ryomuk/TangNano6100MEM/hdl/TangNano6100MEM_project/src/mem_cp.v

// mem_cp.v
// to be included from the top module at the compile

initial
begin
mem_cp['o0000]='o0000;
mem_cp['o0001]='o0000;
mem_cp['o0002]='o0000;
mem_cp['o0003]='o0000;
mem_cp['o0004]='o0000;
mem_cp['o0005]='o0000;
mem_cp['o0006]='o0000;
mem_cp['o0007]='o0000;
mem_cp['o0010]='o0000;
mem_cp['o0011]='o0000;
mem_cp['o0012]='o0000;
mem_cp['o0013]='o0000;
mem_cp['o0014]='o0000;
mem_cp['o0015]='o0000;
mem_cp['o0016]='o0000;
mem_cp['o0017]='o0000;
mem_cp['o0020]='o0000;
mem_cp['o0021]='o0000;
mem_cp['o0022]='o0000;
mem_cp['o0023]='o0000;
mem_cp['o0024]='o0000;
mem_cp['o0025]='o0000;
mem_cp['o0026]='o0000;
mem_cp['o0027]='o0000;
mem_cp['o0030]='o0000;
mem_cp['o0031]='o0000;
mem_cp['o0032]='o0000;
mem_cp['o0033]='o0000;
mem_cp['o0034]='o0000;
mem_cp['o0035]='o0000;
mem_cp['o0036]='o0000;
mem_cp['o0037]='o0000;
mem_cp['o0040]='o0000;
mem_cp['o0041]='o0000;
mem_cp['o0042]='o0000;
mem_cp['o0043]='o0000;
mem_cp['o0044]='o0000;
mem_cp['o0045]='o0000;
mem_cp['o0046]='o0000;
mem_cp['o0047]='o0000;
mem_cp['o0050]='o0000;
mem_cp['o0051]='o0000;
mem_cp['o0052]='o0000;
mem_cp['o0053]='o0000;
mem_cp['o0054]='o0000;
mem_cp['o0055]='o0000;
mem_cp['o0056]='o0000;
mem_cp['o0057]='o0000;
mem_cp['o0060]='o0000;
mem_cp['o0061]='o0000;
mem_cp['o0062]='o0000;
mem_cp['o0063]='o0000;
mem_cp['o0064]='o0000;
mem_cp['o0065]='o0000;
mem_cp['o0066]='o0000;
mem_cp['o0067]='o0000;
mem_cp['o0070]='o0000;
mem_cp['o0071]='o0000;
mem_cp['o0072]='o0000;
mem_cp['o0073]='o0000;
mem_cp['o0074]='o0000;
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
mem_cp['o7764]='o0000;
mem_cp['o7765]='o0000;
mem_cp['o7766]='o0000;
mem_cp['o7767]='o0000;
mem_cp['o7770]='o0000;
mem_cp['o7771]='o0000;
mem_cp['o7772]='o0000;
mem_cp['o7773]='o0000;
mem_cp['o7774]='o0000;
mem_cp['o7775]='o0000;
mem_cp['o7776]='o5000;
mem_cp['o7777]='o5776;
end
