ryomuk/TangNano6100MEM/hdl/TangNano6100MEM_project/src/sdtape.v

// sdtape.v
// Tape reader/puncher emulator using SD/SDHC memory
// by Ryo Mukai
// 2024/05/22: initial version
// 2024/06/19: bugfixed (in S_INIT_ACMD41)
// 2025/09/20: card detect(i_sd_det_n) installed
// 2025/09/25: separate read tape(0GB-)  and write tape(1GB-)
// 2025/10/07: sd_error is ERROR_RESET during reset
// 2026/01/31: modified for IM6100 (i_tape_start_block)
// 2026/02/01: end of tape flag o_tape_eot installed

module sdtape
  #(
    parameter SYS_FRQ = 27_000_000, // system clock frequency(Hz)
    parameter MEM_FRQ =    400_000  // memory clock frequency(Hz)(106k to 1M)
    )
  (
   input	 i_clk,		     // system clock input
   input	 i_reset_n,	     // synchronous reset input, active low
   input	 i_sd_det_n,	     // card detect input, active low
   input	 i_sd_miso,
   output	 o_sd_mosi,
   output	 o_sd_cs_n,
   output	 o_sd_clk,

   output	 o_tape_read_busy,   // PR_BUSY
   output reg	 o_tape_read_done,   // PR_DONE
   output	 o_tape_punch_ready, // PP_READY
   input	 i_tape_read,	     // tape_read
   input	 i_tape_punch,	     // tape_punch
   input	 i_tape_clear_done,  // tape_clear_done
   input [7:0]	 i_tape_punch_data,  // PPBUF
   output [7:0]	 o_tape_read_data,   // PRBUF
   input	 i_tape_flush,	     //
   input [21:0]	 i_tape_start_block,
   input [21:0]	 i_tape_start_block_write,
   input	 i_tape_rewind,
   output	 o_tape_endoftape,
   output [4:0]	 o_sd_state,
   output [3:0]	 o_sd_error,
   output [30:0] o_sd_tape_address,
   output [30:0] o_sd_tape_address_write
   );

  assign o_sd_tape_address       = tape_address; // for debug
  assign o_sd_tape_address_write = tape_address_write; // for debug
  
  reg [30:0]	tape_address;        // 0GB-2GB
  reg [30:0]	tape_address_write;  // 1GB-2GB

  reg [23:0]	sd_block_address;
  reg [23:0]	sd_block_address_write;
  reg [7:0]	tape_read_buf;
  reg [7:0]	tape_punch_buf;

  assign o_tape_read_data = tape_read_buf;
  
  localparam   CLK_DIV  = SYS_FRQ / MEM_FRQ;
  localparam   CLK_DIV2 = CLK_DIV / 2;

  localparam   S_INIT_RESET      = 5'd0;
  localparam   S_INIT_DUMMY      = 5'd1;
  localparam   S_INIT_CMD0       = 5'd2;
  localparam   S_INIT_CMD8       = 5'd3;
  localparam   S_INIT_CMD55      = 5'd4;
  localparam   S_INIT_ACMD41     = 5'd5;
  localparam   S_INIT_ACMD41_RTY = 5'd6;
  localparam   S_INIT_CMD58      = 5'd7;
  localparam   S_INIT_CMD16      = 5'd8;
  localparam   S_IDLE            = 5'd9;
  localparam   S_READ_CMD        = 5'd10; // CMD17
  localparam   S_READ_DATA       = 5'd11;
  localparam   S_WRITE_CMD       = 5'd12; // CMD24
  localparam   S_WRITE_DATA      = 5'd13;
  localparam   S_WRITE_BUSY      = 5'd14;
  localparam   S_WAIT            = 5'd15;
  localparam   S_ERROR           = 5'd16;
  localparam   S_NOCARD          = 5'd17;

  reg [1:0]    sd_version;
  localparam   SD_VERSION1 = 2'd1;
  localparam   SD_VERSION2 = 2'd2;

  reg	       sd_read;
  reg	       sd_write;

  reg	       sd_addressmode_block;
  wire [31:0]  sd_address = sd_addressmode_block ?
	       {8'h0000, sd_block_address[23:0]} :
	       {sd_block_address[22:0], 9'b0};

  wire [31:0]  sd_address_write = sd_addressmode_block ?
	       {8'h0000, sd_block_address_write[23:0]} :
	       {sd_block_address_write[22:0], 9'b0};


  reg [3:0]    sd_error;
  assign o_sd_error = sd_error;
  assign o_sd_state = state;

  localparam   ERROR_NOERROR    = 4'd0;
  localparam   ERROR_CMD0       = 4'd1;
  localparam   ERROR_CMD8       = 4'd2;
  localparam   ERROR_ACMD41     = 4'd3;
  localparam   ERROR_CMD17      = 4'd4;
  localparam   ERROR_CMD24      = 4'd5;
  localparam   ERROR_WRITE_DATA = 4'd6;
  localparam   ERROR_RESET      = 4'd7;
  localparam   ERROR_NOCARD     = 4'd8;
  
  reg [7:0]    mem_readbuf[511:0];
  reg [7:0]    mem_writebuf[511:0];
  
  wire	       clk      = i_clk;
  wire	       reset    = ~i_reset_n | nocard;
  wire	       nocard   = i_sd_det_n;
  wire	       newstate = (state != state_l); // this can occur when clk_cnt==0

  // state
  reg [4:0]    state;
  reg [4:0]    state_l;
  always@(posedge clk)
    state_l <= state;
  
  // reset_cnt
  reg [27:0]   reset_cnt = 0;
  localparam   WIDTH_RESET = (SYS_FRQ / 1000) * 200; // 200ms
  always@(posedge clk)
    if( reset )
      reset_cnt <= 0;
    else if(state == S_INIT_RESET && reset_cnt != WIDTH_RESET)
      reset_cnt <= reset_cnt + 1'd1;

  // clk_cnt
  reg [7:0]    clk_cnt;
  always@(posedge clk)
    if( reset )
      clk_cnt <= 0;
    else if(clk_cnt == CLK_DIV - 1)
      clk_cnt <= 0;
    else
      clk_cnt <= clk_cnt + 1'd1;

  // mem_clk
  reg	       mem_clk;	       
  always@(posedge clk)
    if( reset )
      mem_clk <= 1'b0;
    else if(clk_cnt == CLK_DIV2 - 1)
      mem_clk <= 1'b1;
    else if(clk_cnt == CLK_DIV - 1)
      mem_clk <= 1'b0;

  // dummy_bit_cnt
  reg [9:0]    dummy_bit_cnt;
  localparam   NUM_DUMMY_CLK = 10'd100;
  always@(posedge clk)
    if( newstate )
      dummy_bit_cnt <= 0;
    else if(clk_cnt == CLK_DIV2)
      dummy_bit_cnt <= dummy_bit_cnt + 1'd1;

  // o_sd_clk
  assign o_sd_clk = ( state == S_INIT_RESET
		      || state == S_IDLE
		      || state == S_WAIT
		      )   ? 1'b0 :    mem_clk;

  // send command
  reg [55:0]   send_buf;
  reg [47:0]   command_buf;
  reg	       command_load;
  always@(posedge clk)
    if( reset )
      command_load <= 0;
    else if( newstate )
      command_load <= 1;
    else if((clk_cnt == 1) & command_load) begin
       send_buf <= {8'hff, command_buf};
       command_load <= 0;
    end
    else if(clk_cnt == CLK_DIV - 1) begin
       send_buf[55:0] <= {send_buf[54:0], 1'b1};
    end
  
  // o_sd_cs_n
  assign o_sd_cs_n = (state == S_INIT_RESET
		      || state == S_INIT_DUMMY
		      || state == S_IDLE
		      || state == S_WAIT
		      || state == S_ERROR
		      ) ? 1'b1 : 1'b0;

  // r1
  reg [7:0]    r1_buf;
  reg [3:0]    r1_bit_cnt;
  wire	       r1_received  = r1_bit_cnt[3];
  always@(posedge clk)
    if( newstate )
      r1_bit_cnt <= 0;
    else if(clk_cnt == CLK_DIV2)
      if( ~r1_received )
	if( (r1_bit_cnt != 0) || (i_sd_miso == 0)) begin
	   r1_buf <= {r1_buf[6:0], i_sd_miso};
	   r1_bit_cnt <= r1_bit_cnt + 1'd1;
	end

  // r3, r7
  reg [39:0]   r3_buf;
  reg [5:0]    r3_bit_cnt;
  wire	       r3_received  = (r3_bit_cnt == 6'd40);
  wire [39:0]  r7_buf       = r3_buf;
  wire	       r7_received  = r3_received;
  always@(posedge clk)
    if( newstate )
      r3_bit_cnt <= 0;
    else if(clk_cnt == CLK_DIV2)
      if( ~r3_received )
	if( (r3_bit_cnt != 0) || (i_sd_miso == 0)) begin
	   r3_buf <= {r3_buf[38:0], i_sd_miso};
	   r3_bit_cnt <= r3_bit_cnt + 1'd1;
	end

  // receive data packet
  reg [9:0] read_byte_cnt;
  reg [2:0] read_bit_cnt;
  reg [7:0] read_buf;
  reg	    read_data_done;
  reg	    read_start;
  always@(posedge clk)
    if( state == S_READ_DATA)
      if( newstate ) begin
	 read_byte_cnt <= 0;
	 read_bit_cnt  <= 0;
	 read_start <= 0;
	 read_data_done <= 0;
      end
      else if( read_start ) begin
	 if(clk_cnt == CLK_DIV2)
	   read_buf <= {read_buf[6:0], i_sd_miso};
	 else if(clk_cnt == CLK_DIV2 +1)
   	   if( read_bit_cnt == 3'd7 ) begin
	      read_bit_cnt <= 0;
	      if( ~read_byte_cnt[9]) // read_byte_cnt=0..511
		mem_readbuf[read_byte_cnt] <= read_buf;

	      if(read_byte_cnt == 10'd514) // data(512byte)+CRC(2byte)
		read_data_done <= 1;
	      else
		read_byte_cnt <= read_byte_cnt + 1'd1;
	   end
	   else
	     read_bit_cnt <= read_bit_cnt + 1'd1;
      end
      else if(clk_cnt == CLK_DIV2 +1) // wait for miso==0
	if( i_sd_miso == 0)
	  read_start <= 1'b1;

  // send data packet
  reg [9:0] write_byte_cnt;
  reg [8:0] write_buf_address;
  reg [3:0] write_bit_cnt;
  reg [7:0] write_buf;
  reg	    write_data_done;
  reg [7:0] write_data_response;
  
  always@(posedge clk)
    if( state == S_WRITE_DATA)
      if( newstate ) begin // this can occur when clk_cnt == 0
	 write_byte_cnt  <= 0;
	 write_buf_address <= 0;
	 write_bit_cnt   <= 0;
	 write_data_done <= 0;
      end
      else if(clk_cnt == 1)
	if( write_bit_cnt == 0)
	  case (write_byte_cnt) 
  	    10'd0: write_buf <= 8'b1111_1111;
	    10'd1: write_buf <= 8'b1111_1111;
	    10'd2: write_buf <= 8'b1111_1110;
	    10'd515: write_buf <= 8'b0000_0000; // dummy CRC
	    10'd516: write_buf <= 8'b0000_0000; // dummy CRC
	    10'd517: write_buf <= 8'b1111_1111;
	    10'd518: write_data_done <= 1'b1;
	    default: // byte_cnt = 3..514
	      if(~write_data_done) begin
		 write_buf <= mem_writebuf[write_buf_address];
		 write_buf_address <= write_buf_address + 1'd1;
	      end
	  endcase
	else
	  write_buf <= {write_buf[6:0], 1'b1};
      else if( clk_cnt == CLK_DIV2) begin
	 if(write_byte_cnt == 10'd517) // receive data response
	   write_data_response  <= {write_data_response[6:0], i_sd_miso};
      end
      else if( clk_cnt == CLK_DIV - 1)
	if(write_bit_cnt == 7) begin
	   write_bit_cnt <= 0;
	   write_byte_cnt <= write_byte_cnt + 1'd1;
	end
	else
	  write_bit_cnt <= write_bit_cnt + 1'd1;
  
  // o_sd_mosi
  assign o_sd_mosi = (state == S_WRITE_DATA) ?
		     write_buf[7]:  // data packet
		     send_buf[55];  // command

// command_buf at newstate (clk_cnt == 0)
  always@(posedge clk)
    if( reset )
      command_buf <= 48'hff_ffff_ffff_ff;
    else if( newstate )
      case(state)
	S_INIT_CMD0: command_buf <=  {2'b01, 6'd0,  32'h0,   7'b1001010, 1'b1};
	S_INIT_CMD8: command_buf <=  {2'b01, 6'd8,  32'h1aa, 7'b1000011, 1'b1};
	S_INIT_CMD16: command_buf <= {2'b01, 6'd16, 32'h200, 8'h01};
	S_INIT_CMD55: command_buf <= {2'b01, 6'd55, 32'h0,   8'h01};
	S_INIT_ACMD41:
	  command_buf <= (sd_version == SD_VERSION1) ?
			 {2'b01, 6'd41, 32'h00000000, 8'h01} :
			 {2'b01, 6'd41, 32'h40000000, 8'h01};
	S_INIT_CMD58:  command_buf <= {2'b01, 6'd58, 32'h0, 8'h01};
	S_READ_CMD:    command_buf <= {2'b01, 6'd17, sd_address, 8'h01};
	S_WRITE_CMD:   command_buf <= {2'b01, 6'd24, sd_address_write, 8'h01};
	default:
	  command_buf <= 48'hff_ffff_ffff_ff;
      endcase

  localparam TS_WAIT           = 3'd0;
  localparam TS_IDLE           = 3'd1;
  localparam TS_READ           = 3'd2;
  localparam TS_READ_BUF       = 3'd3;
  localparam TS_READ_BUF_WAIT  = 3'd4;
  localparam TS_PUNCH          = 3'd5;
  localparam TS_WRITE_BUF      = 3'd6;
  localparam TS_WRITE_BUF_WAIT = 3'd7;

  reg [2:0]  tape_state;
  wire [8:0] tape_buf_address = tape_address[8:0];

  // pseudo end of tape detect
  localparam  EOT_SEQZERO = 12'd1024;
  reg [11:0] cnt_seqzero;
  reg	     tape_eot;
  assign     o_tape_endoftape = tape_eot;
    
  assign o_tape_read_busy   = (tape_state != TS_IDLE) | reset;
  assign o_tape_punch_ready = (tape_state == TS_IDLE) & ~reset;
  
  always@(posedge clk)
    if( reset | i_tape_rewind) begin
       o_tape_read_done   <= 0;
       tape_address       <= {i_tape_start_block,       9'b000_000_000};
       tape_address_write <= {i_tape_start_block_write, 9'b000_000_000};
       tape_state <= TS_WAIT;
       sd_read <= 0;
       sd_write <= 0;
       {tape_eot, cnt_seqzero} <= 0;
    end
    else begin
       sd_block_address       <=  tape_address[30:9];
       sd_block_address_write <=  tape_address_write[30:9];
       case( tape_state )
	 TS_WAIT:
	   if( (state == S_IDLE) &
	       (~i_tape_read) &
	       (~i_tape_punch) &
	       (~i_tape_flush))
	     tape_state <= TS_IDLE;
	 
	 TS_IDLE: begin
	    if( i_tape_read )
	      if( tape_buf_address == 9'b0 )
		tape_state <= TS_READ_BUF;
	      else
		tape_state <= TS_READ;
	    else if( i_tape_punch ) begin
	       tape_punch_buf <= i_tape_punch_data;
	       tape_state <= TS_PUNCH;
	    end
	    else if( i_tape_flush )
	      tape_state <= TS_WRITE_BUF;
	    
	    if( i_tape_read )
	      o_tape_read_done <= 0;
	    
	    if( i_tape_clear_done)
	      o_tape_read_done <= 0;
	 end
	 
	 TS_READ: begin
	    tape_read_buf <= mem_readbuf[tape_buf_address];
	    mem_writebuf[tape_buf_address] <= mem_readbuf[tape_buf_address];
	    tape_address <= tape_address + 1'd1;
	    o_tape_read_done <= 1;
	    tape_state <= TS_WAIT;

	    // count consecutive zeros
	    if( cnt_seqzero == EOT_SEQZERO )
	      tape_eot <= 1'b1;
	    else if(mem_readbuf[tape_buf_address] == 8'b0)
	      cnt_seqzero <= cnt_seqzero + 1'b1;
	    else
	      cnt_seqzero <= 0;
	 end
	 
	 TS_READ_BUF:
	   if( state == S_IDLE )
	     sd_read <= 1'b1;
	   else if(state == S_READ_CMD) begin
	      sd_read <= 1'b0;
	      tape_state <= TS_READ_BUF_WAIT;
	   end
	   else
	     sd_read <= 1'b0;
	 
	 TS_READ_BUF_WAIT:
	   if( state == S_IDLE)
	     tape_state <= TS_READ;
	 
	 TS_PUNCH: begin
	    mem_writebuf[tape_buf_address] <= tape_punch_buf;
	    if( tape_buf_address == 9'h1ff )
	      tape_state <= TS_WRITE_BUF;
	    else
	      tape_state <= TS_WAIT;

	    tape_address_write <= tape_address_write + 1'b1;
	 end
	 
	 TS_WRITE_BUF:
	   if( state == S_IDLE )
	     sd_write <= 1'b1;
	   else if(state == S_WRITE_CMD) begin
	      sd_write<= 1'b0;
	      tape_state <= TS_WAIT;
	   end
	   else
	     sd_write <= 1'b0;
	 
	 default:;
       endcase
    end

  always@(posedge clk)
    if( reset ) begin
       if( nocard )
	 sd_error <= ERROR_NOCARD;
       else
	 sd_error <= ERROR_RESET;
	 state <= S_INIT_RESET;
    end
    else if(clk_cnt == CLK_DIV -1) // state change at (clk_cnt=CLK_DIV -1)
      case(state)
	S_INIT_RESET: begin
	   sd_version <= SD_VERSION1;
	   sd_error <= ERROR_RESET;
	   sd_addressmode_block <= 0;
	   if(reset_cnt == WIDTH_RESET) // wait on reset
	     state <= S_INIT_DUMMY;
	end

	S_INIT_DUMMY: // send dummy clock
	  if(dummy_bit_cnt == NUM_DUMMY_CLK)
	    state <= S_INIT_CMD0;

	S_INIT_CMD0: // send CMD0
	  if( r1_received )
	    if(r1_buf == 8'b1)
	      state <= S_INIT_CMD8;
	    else
	      {state, sd_error} <= {S_ERROR, ERROR_CMD0};

	S_INIT_CMD8:
	  if( r7_received ) begin
	     state <= S_INIT_CMD55;
	     if(r7_buf[11:0] == 12'h1aa)
	       sd_version <= SD_VERSION2;
	  end
	       
	S_INIT_CMD55:
	  if( r1_received )
	    state <= S_INIT_ACMD41;

	S_INIT_ACMD41:
	  if( r1_received )
	    if( r1_buf == 8'b0 )
	      if( sd_version == SD_VERSION1)
		 state <= S_INIT_CMD16;
	      else // version 2
		state <= S_INIT_CMD58;
	    else if( r1_buf == 8'b1 )
	      state <= S_INIT_ACMD41_RTY;
	    else 
	      {state, sd_error} <= {S_ERROR, ERROR_ACMD41};
	
	S_INIT_ACMD41_RTY:
	   state <= S_INIT_CMD55;
	
	S_INIT_CMD58:
	  if( r3_received )
	    if( r3_buf[30] == 1'b1 ) begin // sdhc and sdxc
	       sd_addressmode_block <= 1'b1;
	       state <= S_IDLE;
	    end
	    else  // sdsc
	      state <= S_INIT_CMD16;

	S_INIT_CMD16:
	  if( r1_received )
	    if( r1_buf == 8'b0 )
	       state <= S_IDLE;

	S_IDLE: begin
	   sd_error <= ERROR_NOERROR;
	   if( sd_read )
	     state <= S_READ_CMD;
	   else if( sd_write )
	     state <= S_WRITE_CMD;
	   end
	S_READ_CMD:
	  if( r1_received )
	    if( r1_buf == 8'b0 )
	      state <= S_READ_DATA;
	    else
	      {state, sd_error} <= {S_ERROR, ERROR_CMD17};
	
	S_READ_DATA:
	  if( read_data_done )
	    state <= S_WAIT;

	S_WRITE_CMD:
	  if( r1_received )
	    if( r1_buf == 8'b0 )
	       state <= S_WRITE_DATA;
	    else
	       {state, sd_error} <= {S_ERROR, ERROR_CMD24};
	
	S_WRITE_DATA:
	  if( write_data_done )
	    if( write_data_response[4:0] == 5'b0_010_1)
	      state <= S_WRITE_BUSY;
	    else
	      {state, sd_error} <= {S_ERROR, ERROR_WRITE_DATA};

	S_WRITE_BUSY:
	  if( i_sd_miso )
	    state <= S_WAIT;
	
	S_WAIT:
	  if( ~sd_read & ~sd_write)
	    state <= S_IDLE;

	S_ERROR:;

	default:;
      endcase

endmodule 
